mycelialdesigns/Plaice/cad/stubsocketarray.FCStd

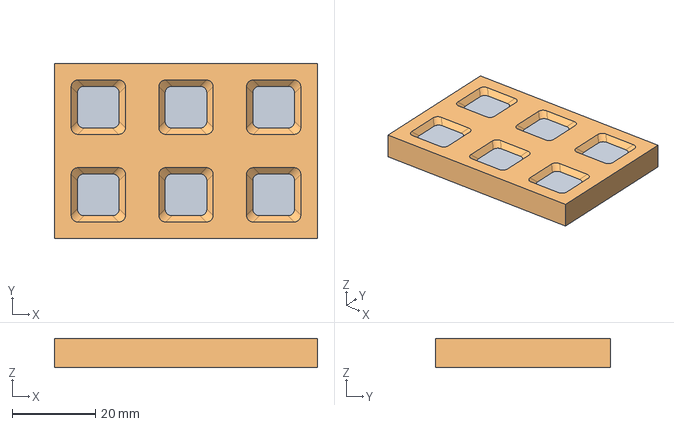
[picture p164: CAD file, 2026-07-09]
cad/stubsocketarray.FCStd
63.0 x 42.0 x 7.00 mm
stubsocketarray
plate_bare001
