mycelialdesigns/Plaice/cad/slide_intruding_xy.FCStd

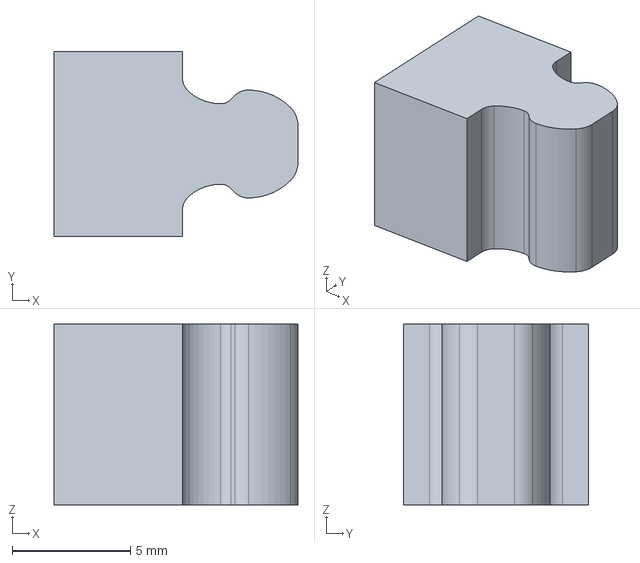
[picture p165: CAD file, 2026-07-09]
cad/slide_intruding_xy.FCStd
10.3 x 7.80 x 7.62 mm
