mycelialdesigns/Plaice/cad/cornerstackingcap.FCStd

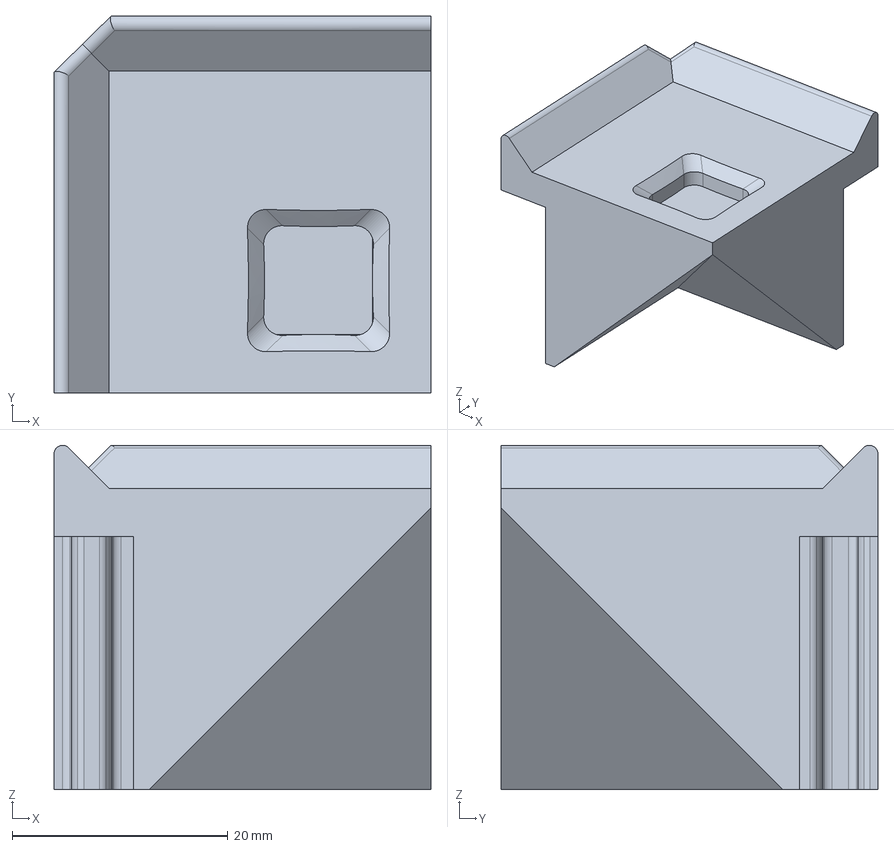
[picture p166: CAD file, 2026-07-09]
cad/cornerstackingcap.FCStd
34.9 x 34.9 x 31.9 mm
