mycelialdesigns/Plaice/cad/slide_protruding_xy.FCStd

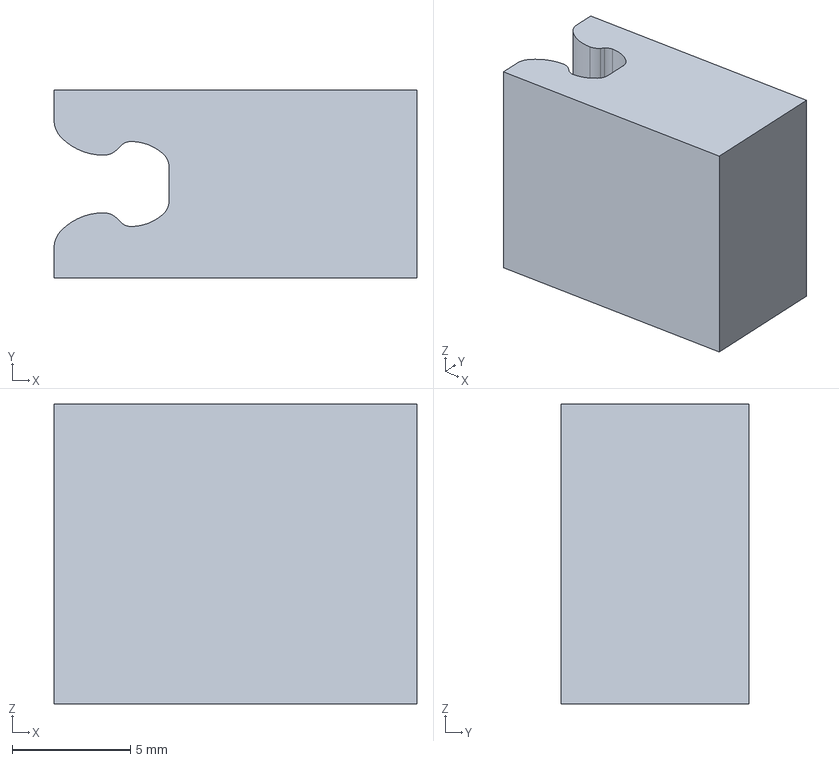
[picture p167: CAD file, 2026-07-09]
cad/slide_protruding_xy.FCStd
15.4 x 7.96 x 12.7 mm
