mycelialdesigns/Plaice/cad/corner.FCStd

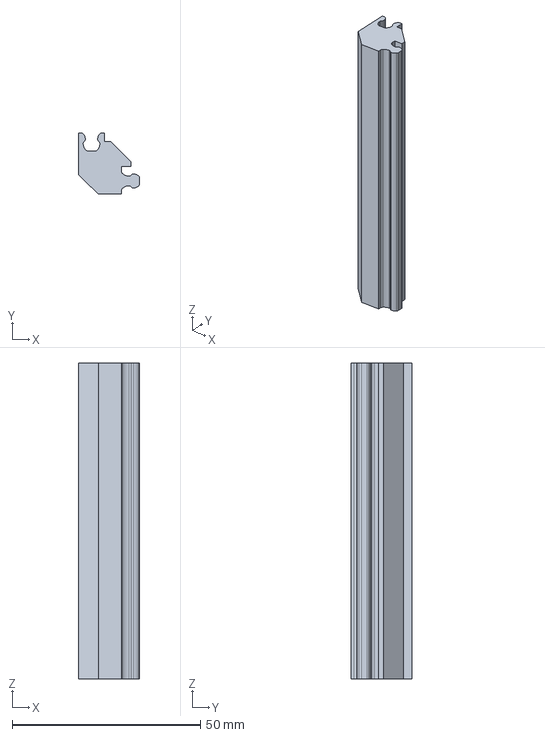
[picture p168: CAD file, 2026-07-09]
cad/corner.FCStd
16.3 x 16.3 x 83.8 mm
