mycelialdesigns/Plaice/cad/plug.FCStd

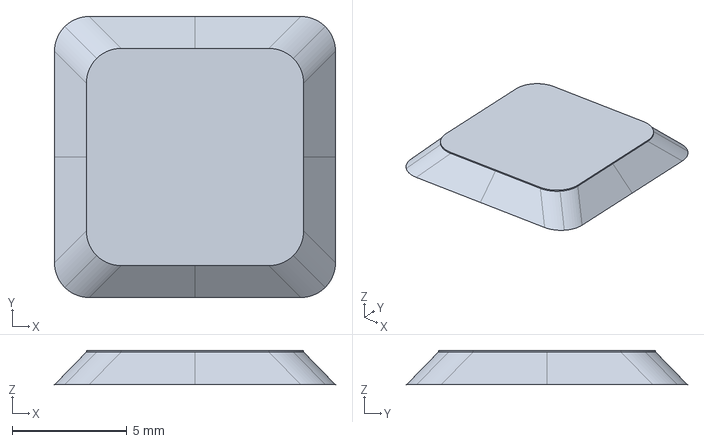
[picture p169: CAD file, 2026-07-09]
cad/plug.FCStd
12.3 x 12.3 x 1.50 mm
