mycelialdesigns/Plaice/cad/plug_nubbed_array.FCStd

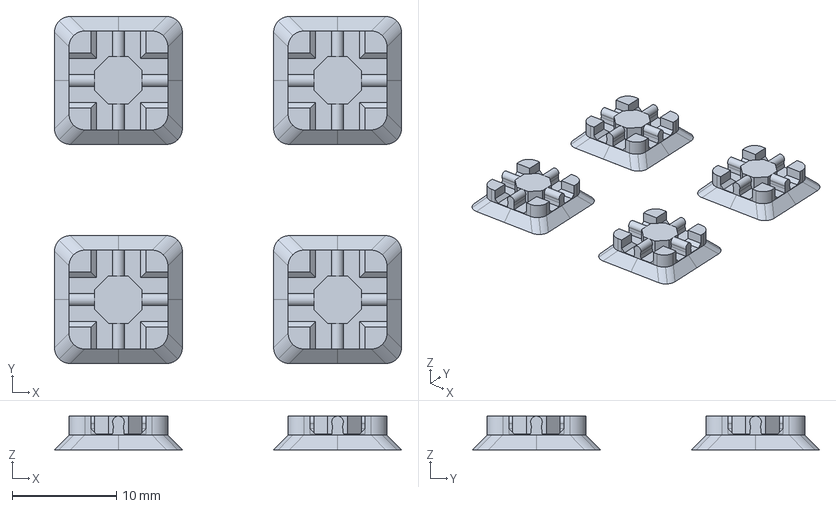
[picture p170: CAD file, 2026-07-09]
cad/plug_nubbed_array.FCStd
33.3 x 33.3 x 3.24 mm
