mycelialdesigns/Plaice/cad/cross_glide.FCStd

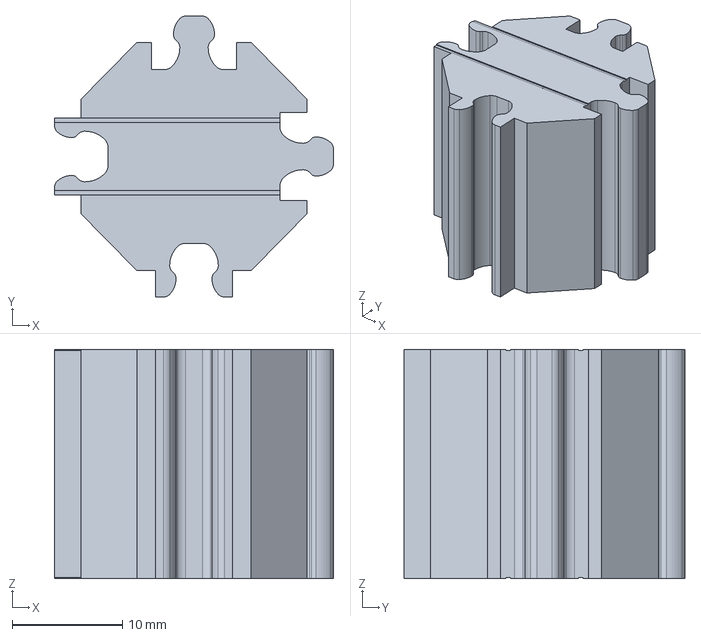
[picture p171: CAD file, 2026-07-09]
cad/cross_glide.FCStd
25.4 x 25.5 x 20.8 mm
