mycelialdesigns/Plaice/cad/tee_slide_intruding.FCStd

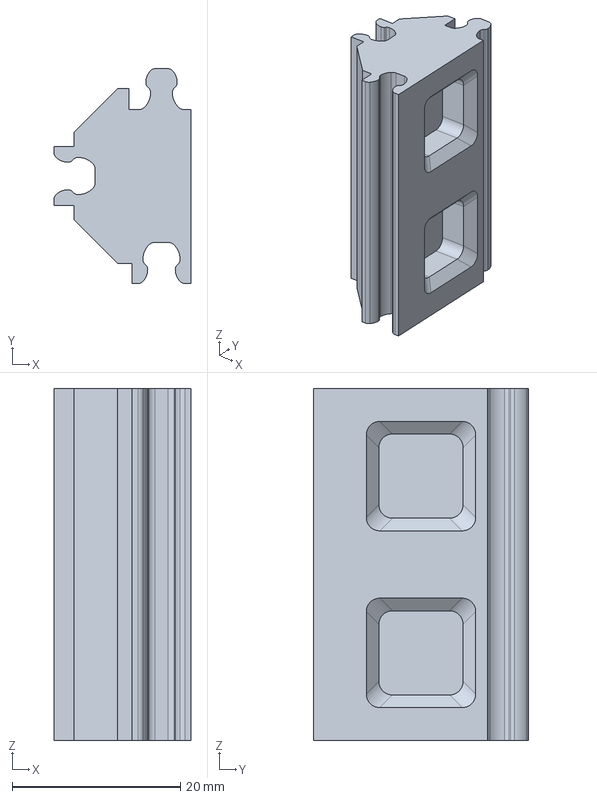
[picture p172: CAD file, 2026-07-09]
cad/tee_slide_intruding.FCStd
16.3 x 25.5 x 41.8 mm
