mycelialdesigns/Plaice/cad/cornerstackingcap_thin.FCStd

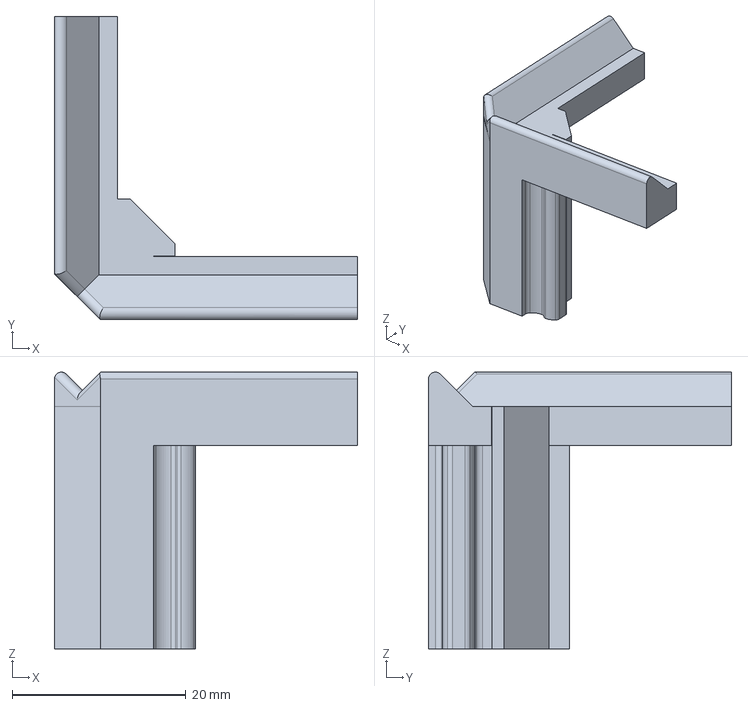
[picture p173: CAD file, 2026-07-09]
cad/cornerstackingcap_thin.FCStd
34.9 x 34.9 x 31.9 mm
