mycelialdesigns/Plaice/cad/plug_nubbed.FCStd

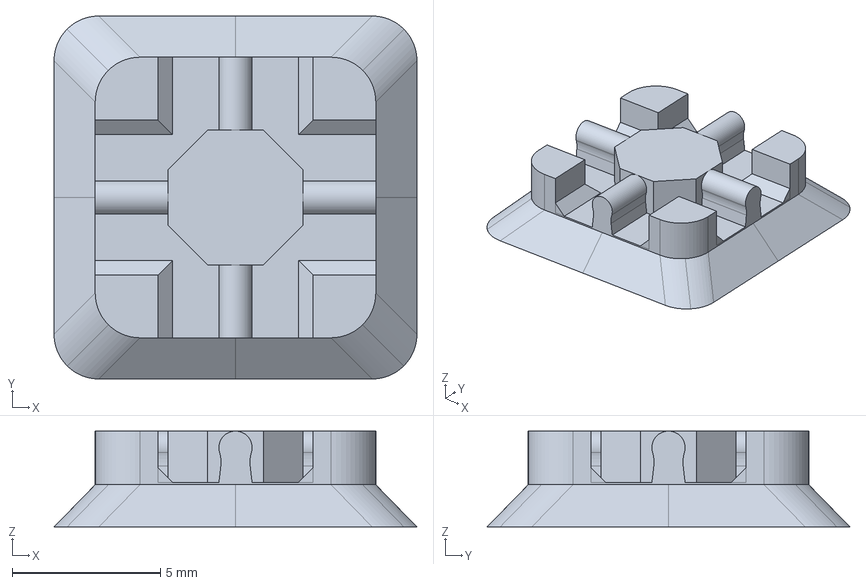
[picture p174: CAD file, 2026-07-09]
cad/plug_nubbed.FCStd
12.3 x 12.3 x 3.24 mm
