mycelialdesigns/Plaice/cad/stackinglip_intruding.FCStd

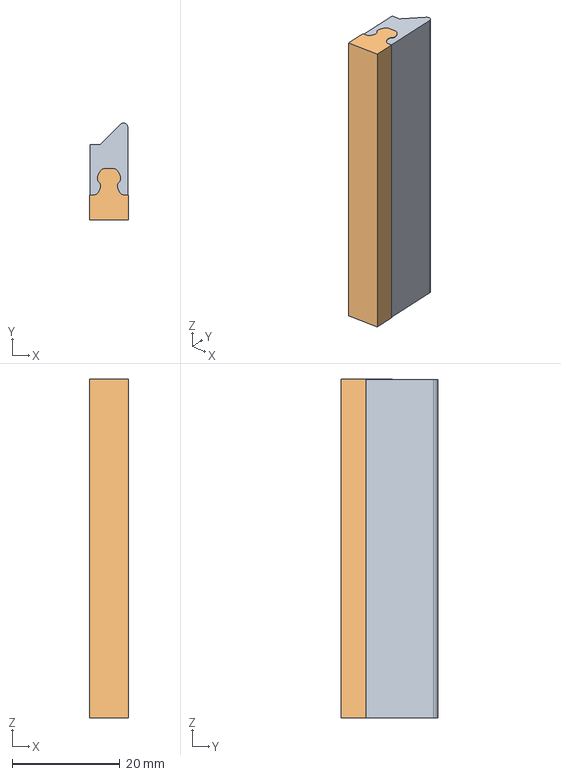
[picture p175: CAD file, 2026-07-06]
cad/stackinglip_intruding.FCStd
7.30 x 18.0 x 63.0 mm
stackinglip_intruding
subtractive
