mycelialdesigns/Plaice/cad/cover_clipped.FCStd

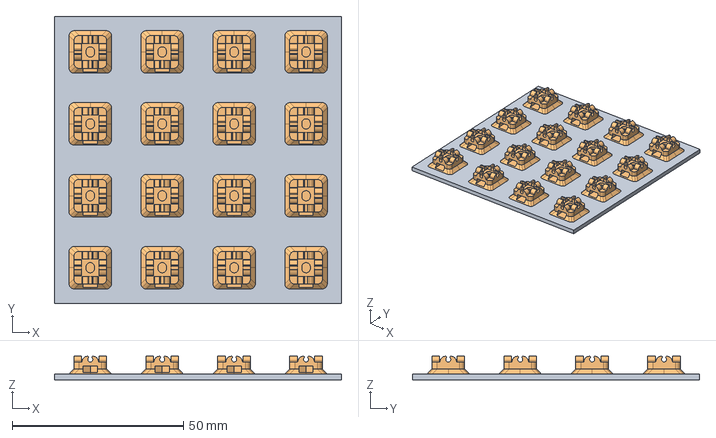
[picture p176: CAD file, 2026-07-06]
cad/cover_clipped.FCStd
83.8 x 83.8 x 6.90 mm
cover_clipped
plug_clipped_array
