mycelialdesigns/Plaice/cad/cornercap_outside.FCStd

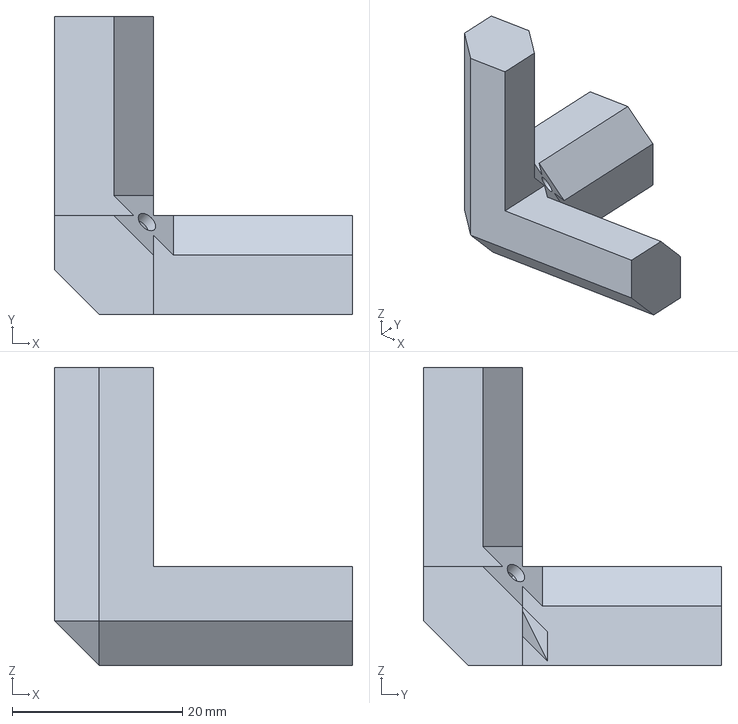
[picture p177: CAD file, 2026-07-06]
cad/cornercap_outside.FCStd
35.0 x 35.0 x 35.0 mm
