mycelialdesigns/Plaice/cad/beam_thru_printable.FCStd

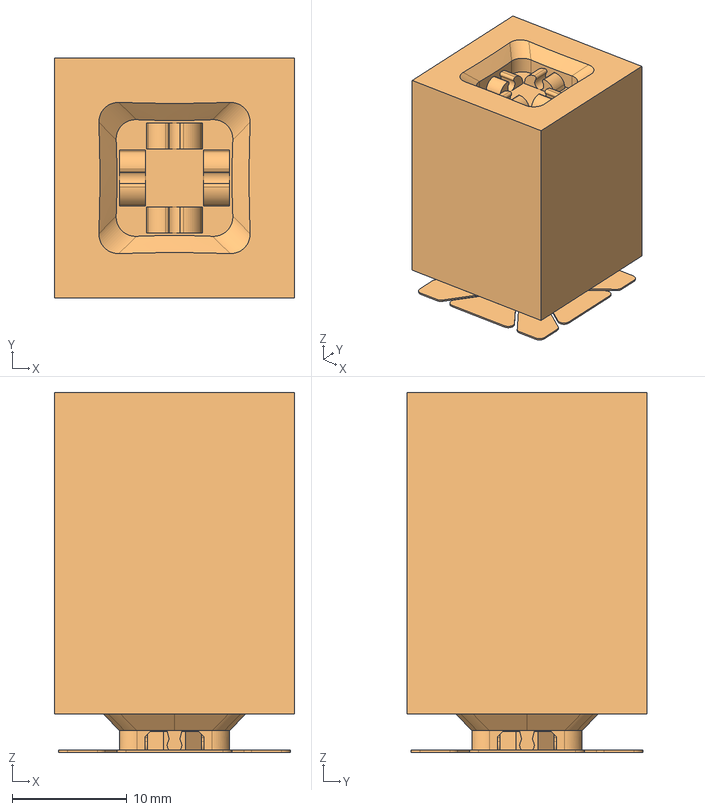
[picture p178: CAD file, 2026-07-06]
cad/beam_thru_printable.FCStd
20.9 x 20.9 x 31.4 mm
beam_thru_printable
beam_printable002
