mycelialdesigns/Plaice/cad/plug_clipped_array.FCStd

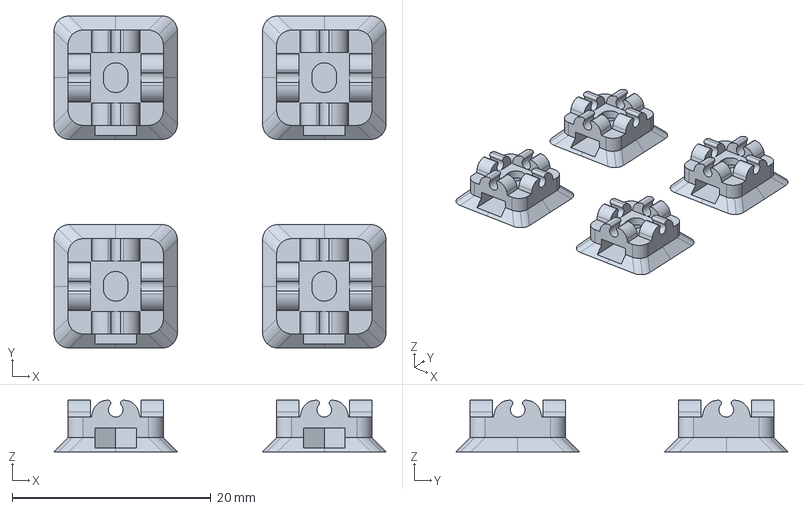
[picture p179: CAD file, 2026-07-06]
cad/plug_clipped_array.FCStd
33.4 x 33.4 x 5.20 mm
