mycelialdesigns/Plaice/cad/nubmouseears_array.FCStd

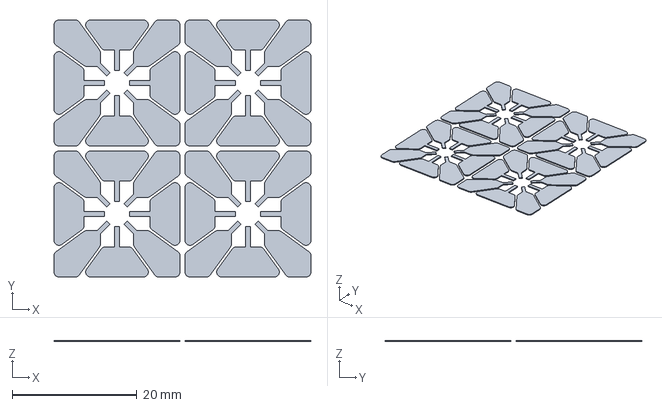
[picture p180: CAD file, 2026-07-06]
cad/nubmouseears_array.FCStd
41.2 x 41.2 x 0.2 mm
