mycelialdesigns/Plaice/cad/tee_glide_protruding_printable.FCStd

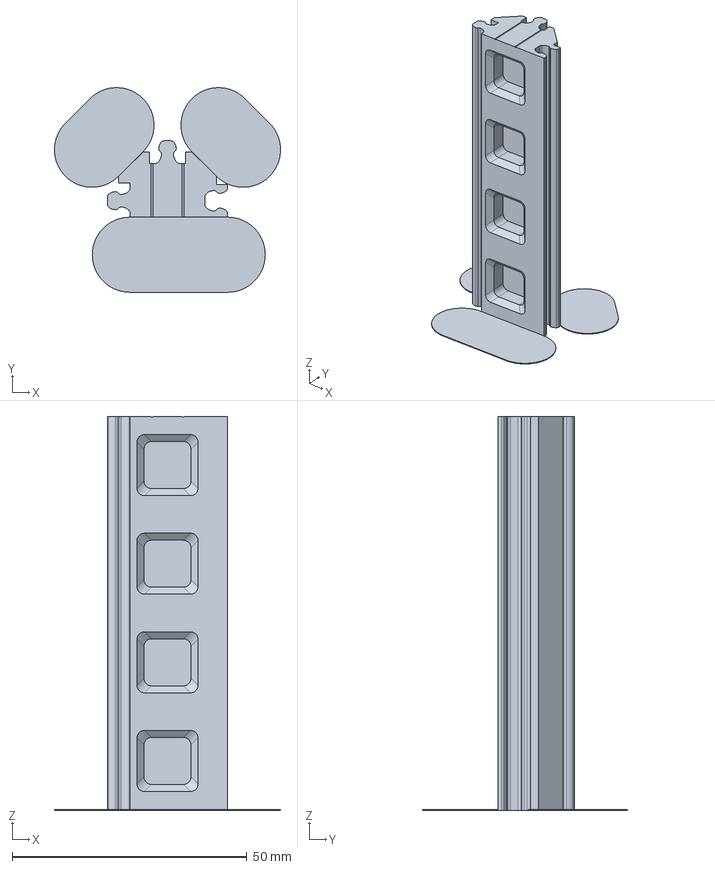
[picture p181: CAD file, 2026-07-06]
cad/tee_glide_protruding_printable.FCStd
48.1 x 43.6 x 83.9 mm
