mycelialdesigns/Plaice/cad/beam.FCStd

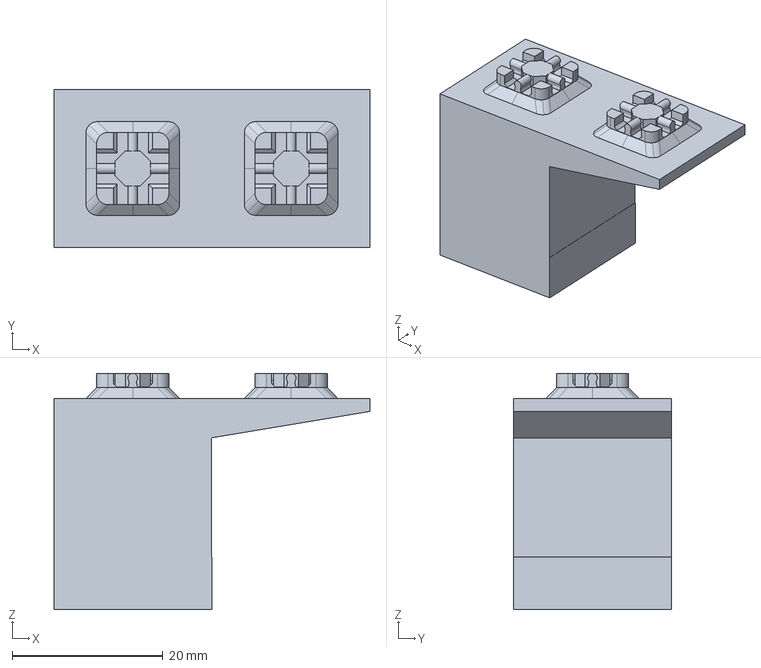
[picture p182: CAD file, 2026-07-06]
cad/beam.FCStd
41.9 x 20.9 x 31.4 mm
