mycelialdesigns/Plaice/cad/slide_intruding.FCStd

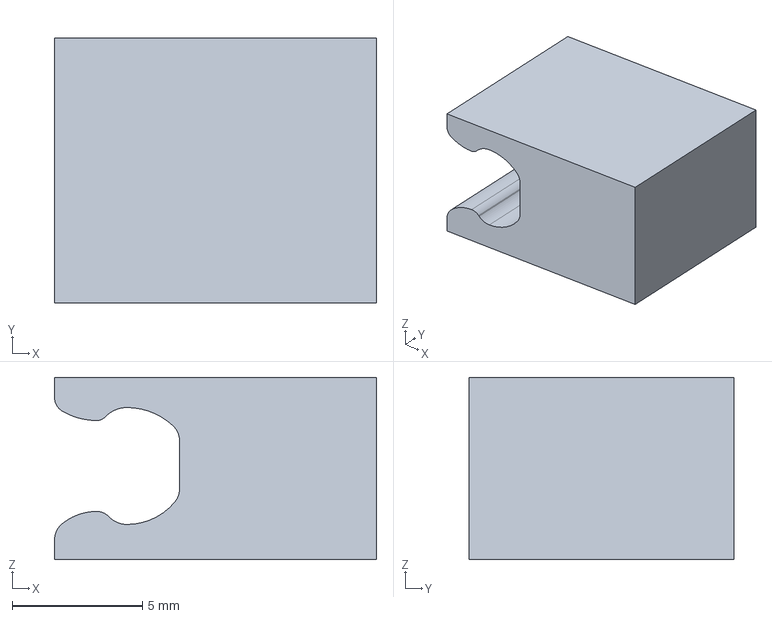
[picture p183: CAD file, 2026-07-06]
cad/slide_intruding.FCStd
12.4 x 10.2 x 7.00 mm
