mycelialdesigns/Plaice/cad/hinge.FCStd

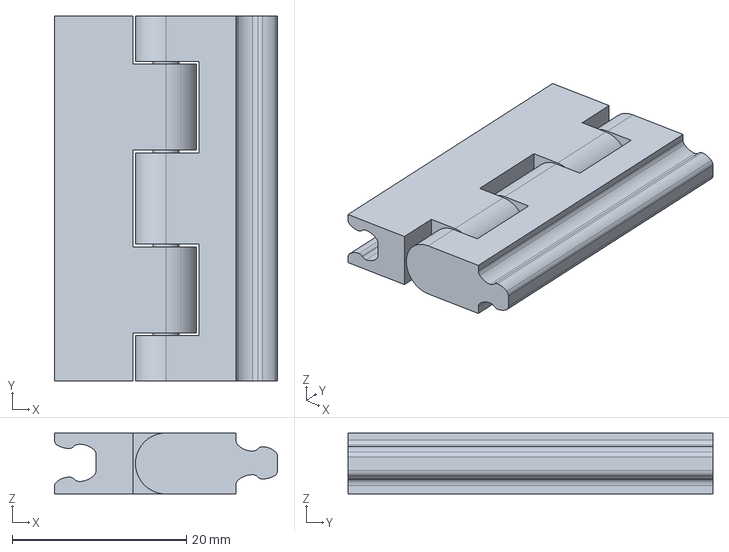
[picture p184: CAD file, 2026-07-06]
cad/hinge.FCStd
25.7 x 41.9 x 7.00 mm
