mycelialdesigns/Plaice/cad/tee_mouseears.FCStd

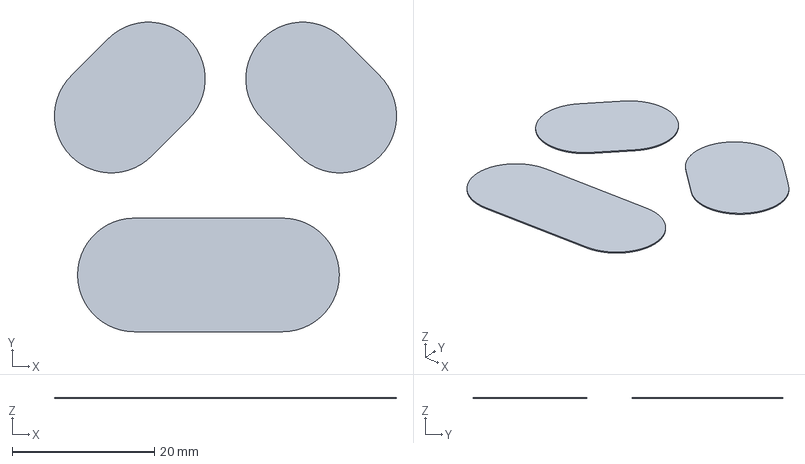
[picture p185: CAD file, 2026-07-06]
cad/tee_mouseears.FCStd
48.1 x 43.6 x 0.2 mm
