mycelialdesigns/Plaice/cad/corner_printable.FCStd

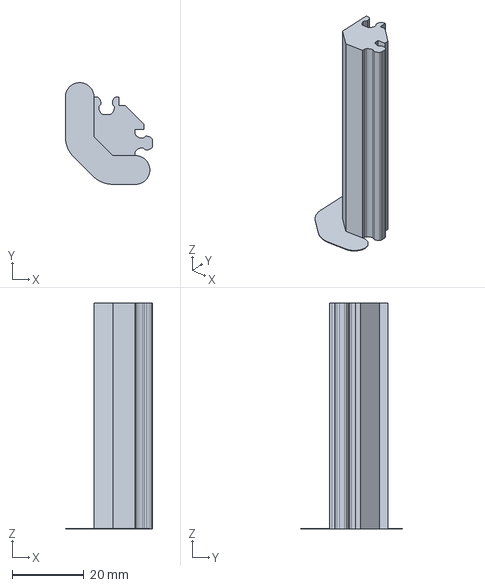
[picture p186: CAD file, 2026-07-06]
cad/corner_printable.FCStd
24.3 x 28.3 x 62.9 mm
