mycelialdesigns/Plaice/cad/plate_overmold_side.FCStd

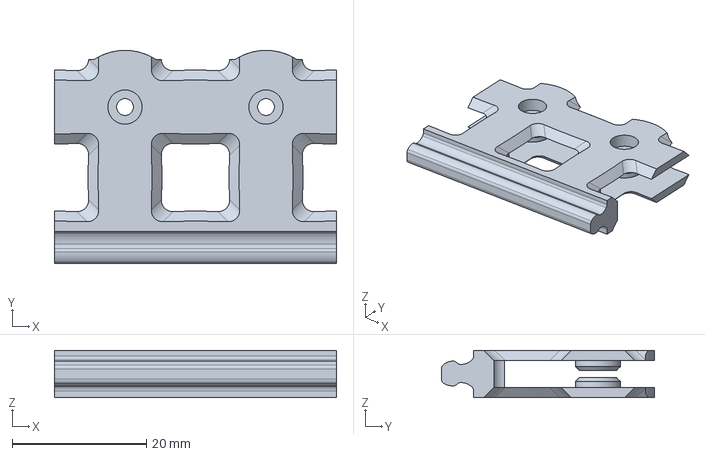
[picture p187: CAD file, 2026-07-06]
cad/plate_overmold_side.FCStd
42.0 x 31.8 x 7.00 mm
