mycelialdesigns/Plaice/cad/tee_glide_intruding_printable.FCStd

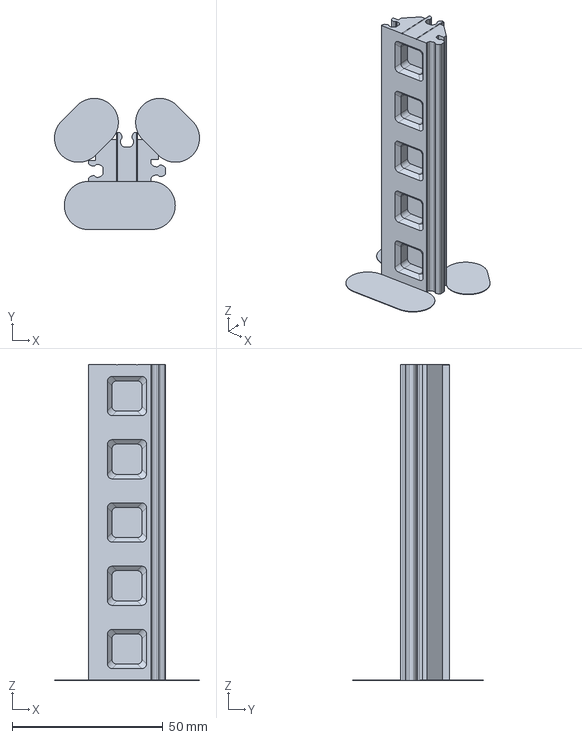
[picture p188: CAD file, 2026-07-06]
cad/tee_glide_intruding_printable.FCStd
48.1 x 43.6 x 104.9 mm
