mycelialdesigns/Plaice/cad/lasercut.FCStd

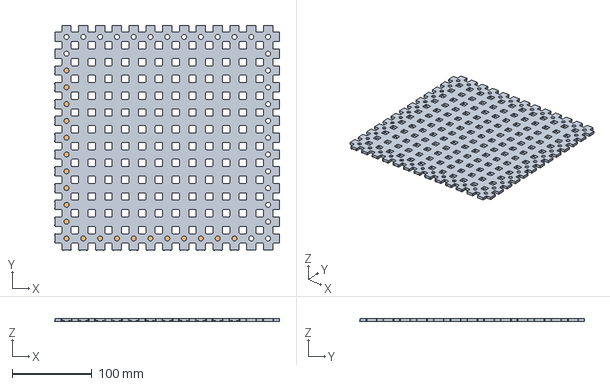
[picture p189: CAD file, 2026-07-06]
cad/lasercut.FCStd
281.3 x 281.3 x 4.00 mm
middle
top
