mycelialdesigns/Plaice/cad/tee_slide_intruding_printable.FCStd

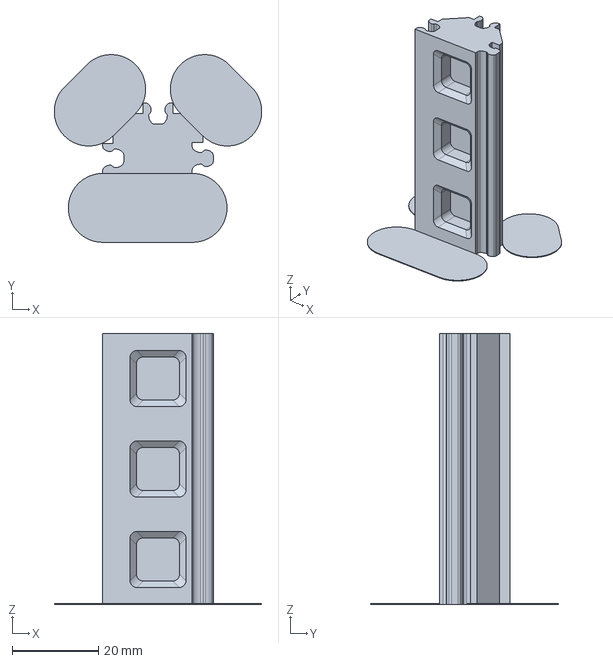
[picture p190: CAD file, 2026-07-06]
cad/tee_slide_intruding_printable.FCStd
48.1 x 43.6 x 62.9 mm
