mycelialdesigns/Plaice/cad/stackingpeg.FCStd

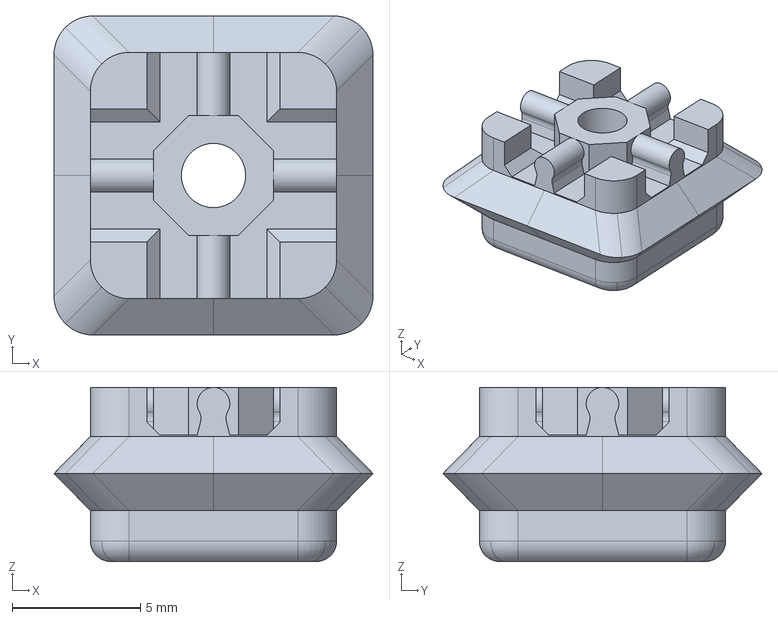
[picture p191: CAD file, 2026-07-06]
cad/stackingpeg.FCStd
12.4 x 12.4 x 6.78 mm
