mycelialdesigns/Plaice/cad/plate_routed.FCStd

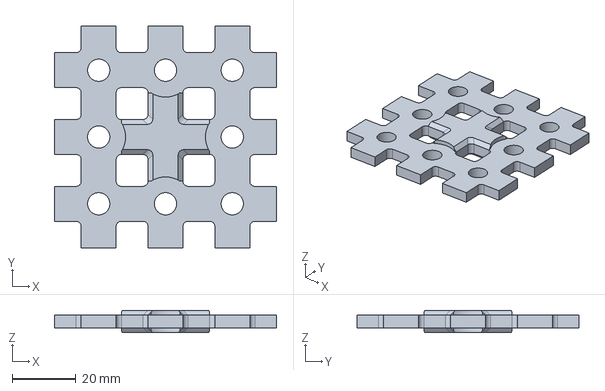
[picture p192: CAD file, 2026-07-06]
cad/plate_routed.FCStd
69.8 x 69.8 x 7.00 mm
