mycelialdesigns/Plaice/cad/manualrouterjigs.FCStd

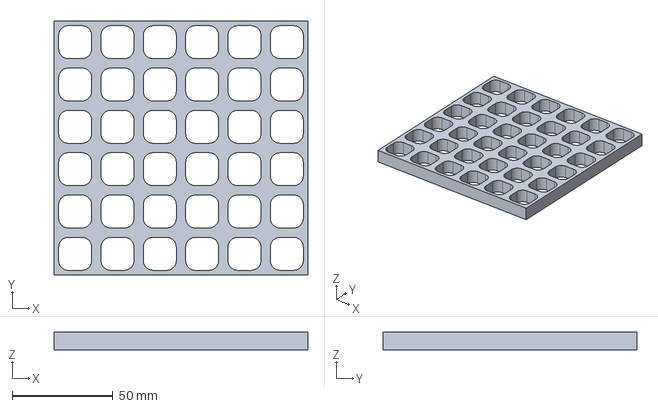
[picture p193: CAD file, 2026-07-06]
cad/manualrouterjigs.FCStd
126.0 x 126.0 x 8.89 mm
