mycelialdesigns/Plaice/cad/plate_overmold_corner.FCStd

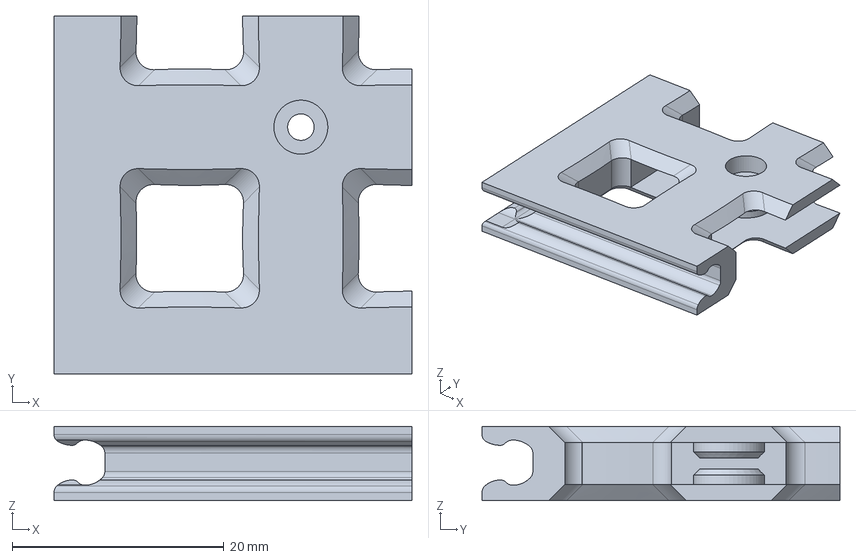
[picture p194: CAD file, 2026-07-06]
cad/plate_overmold_corner.FCStd
33.8 x 33.8 x 7.00 mm
