mycelialdesigns/Plaice/cad/beam_printable.FCStd

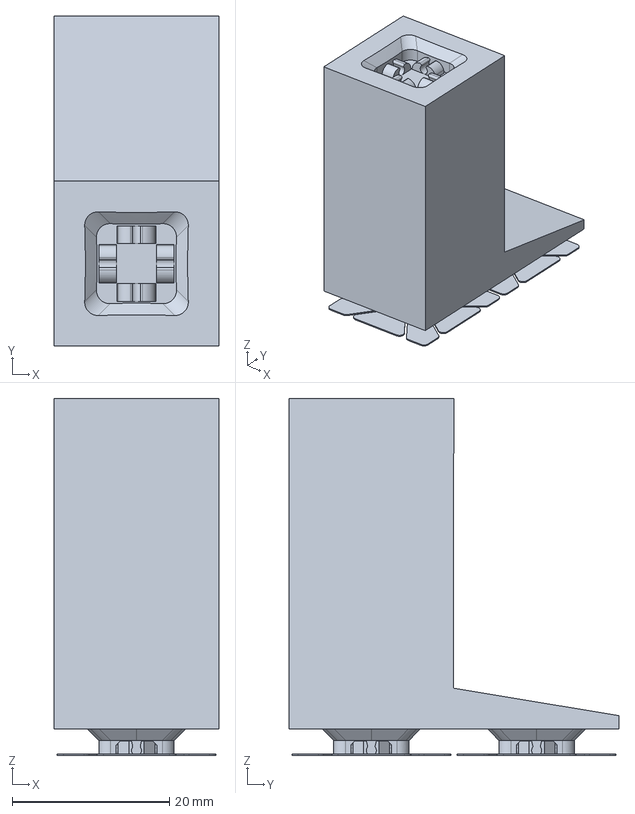
[picture p195: CAD file, 2026-07-06]
cad/beam_printable.FCStd
20.9 x 41.9 x 45.4 mm
