mycelialdesigns/Plaice/cad/backing_nubbed.FCStd

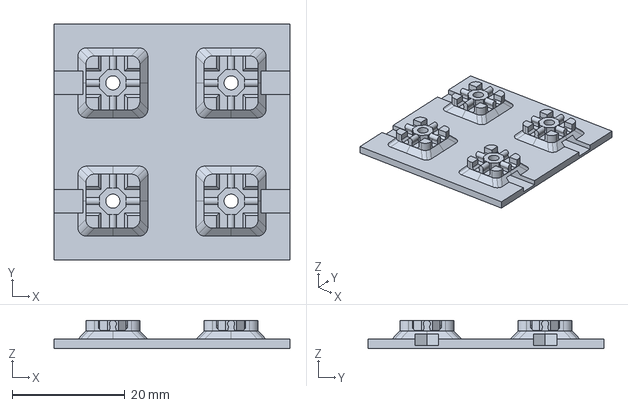
[picture p196: CAD file, 2026-07-06]
cad/backing_nubbed.FCStd
41.9 x 41.9 x 5.05 mm
