mycelialdesigns/Plaice/cad/backing_clipped.FCStd

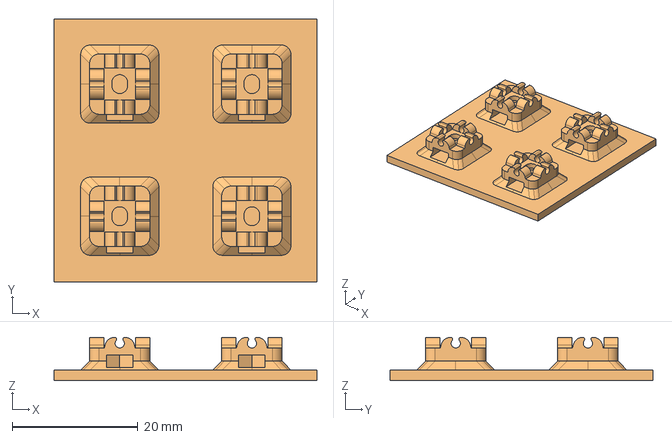
[picture p197: CAD file, 2026-07-06]
cad/backing_clipped.FCStd
41.8 x 41.8 x 6.90 mm
backing_clipped
cover_clipped001
