mycelialdesigns/Plaice/cad/cover_nubbed.FCStd

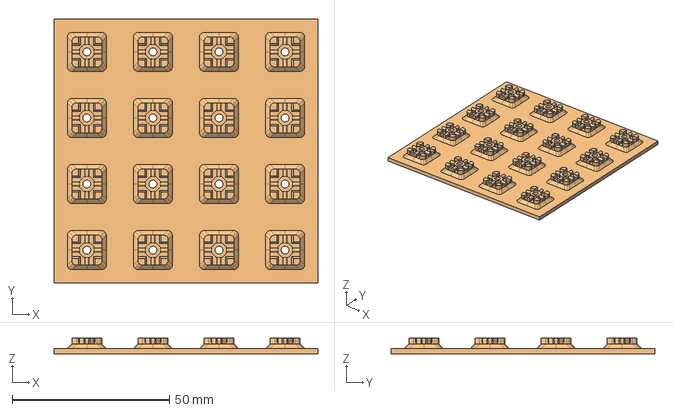
[picture p198: CAD file, 2026-07-06]
cad/cover_nubbed.FCStd
83.9 x 83.9 x 5.05 mm
cover_nubbed
cover_nubbed_base001
