mycelialdesigns/Plaice/cad/cornercap_inside.FCStd

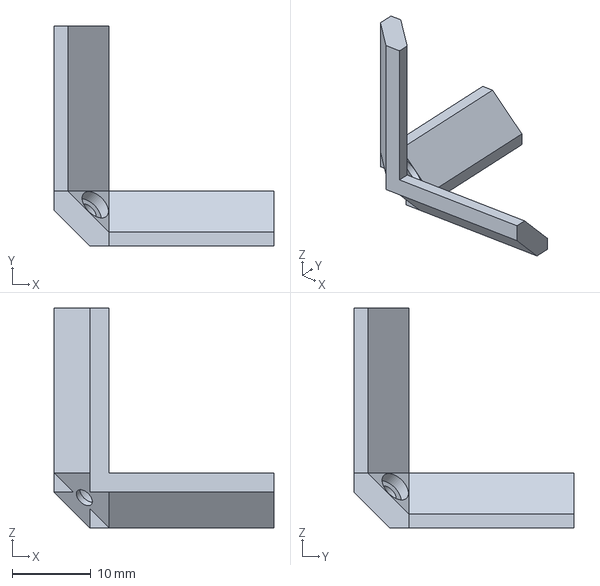
[picture p199: CAD file, 2026-07-06]
cad/cornercap_inside.FCStd
28.0 x 28.0 x 28.0 mm
