mycelialdesigns/Plaice/cad/tee_slide_protruding_printable.FCStd

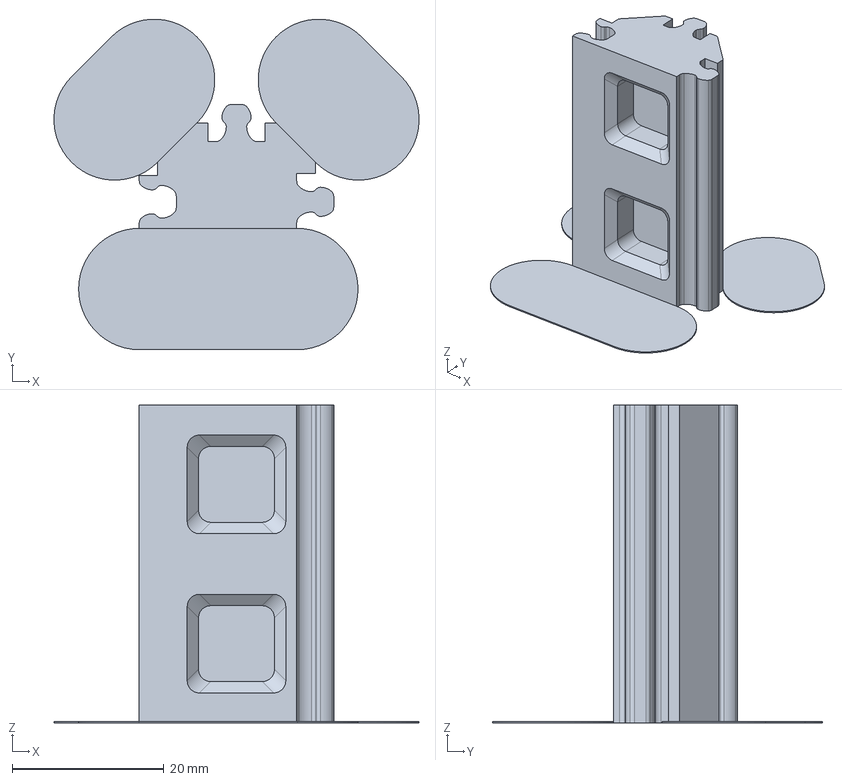
[picture p200: CAD file, 2026-07-06]
cad/tee_slide_protruding_printable.FCStd
48.1 x 43.6 x 41.9 mm
