mycelialdesigns/Plaice/cad/plug_clipped.FCStd

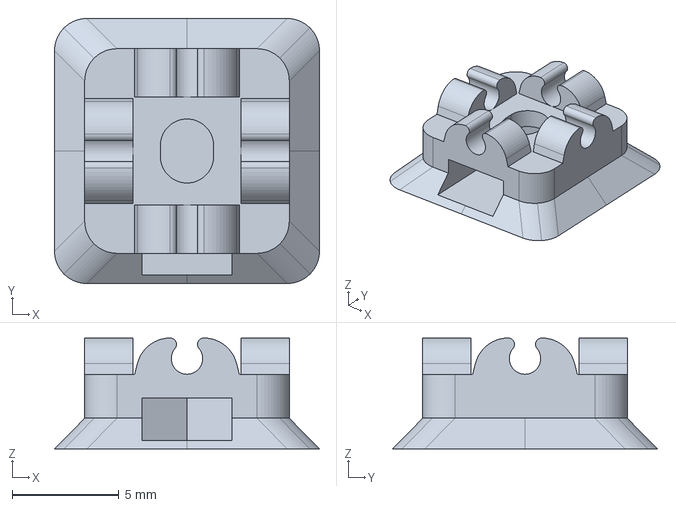
[picture p201: CAD file, 2026-07-06]
cad/plug_clipped.FCStd
12.4 x 12.4 x 5.20 mm
