mycelialdesigns/Plaice/cad/stackinglip_base.FCStd

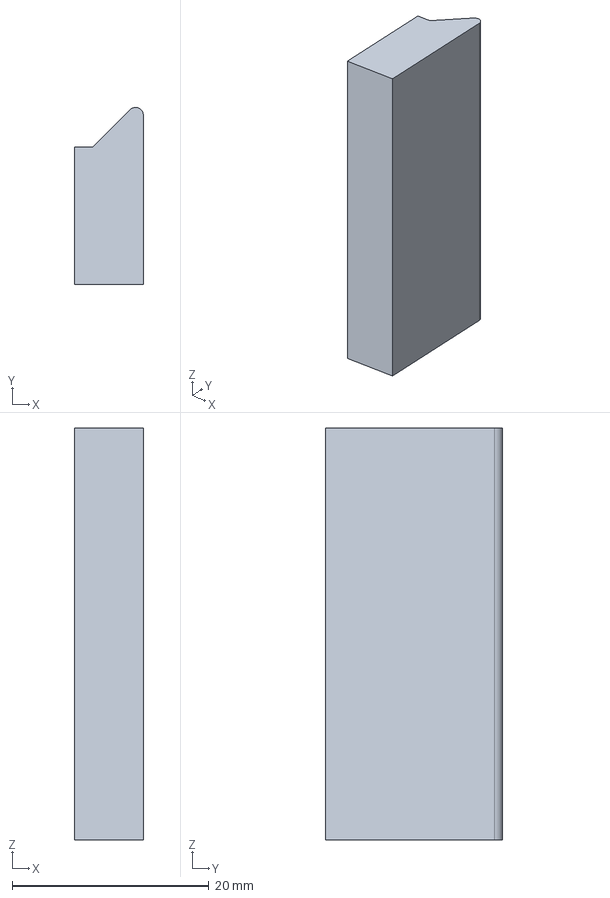
[picture p202: CAD file, 2026-07-06]
cad/stackinglip_base.FCStd
7.00 x 18.0 x 41.9 mm
