mycelialdesigns/Plaice/cad/nubmouseears.FCStd

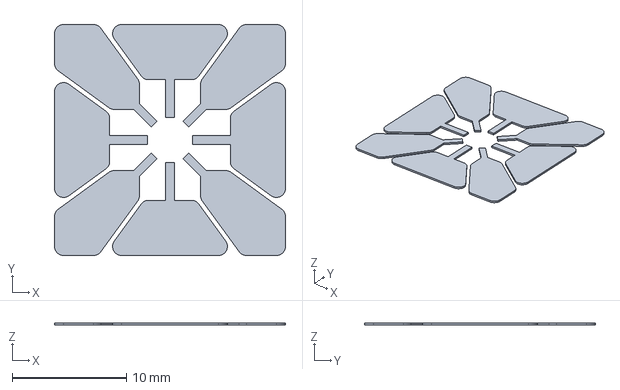
[picture p203: CAD file, 2026-07-06]
cad/nubmouseears.FCStd
20.2 x 20.2 x 0.2 mm
