mycelialdesigns/Plaice/cad/stackinglip_protruding.FCStd

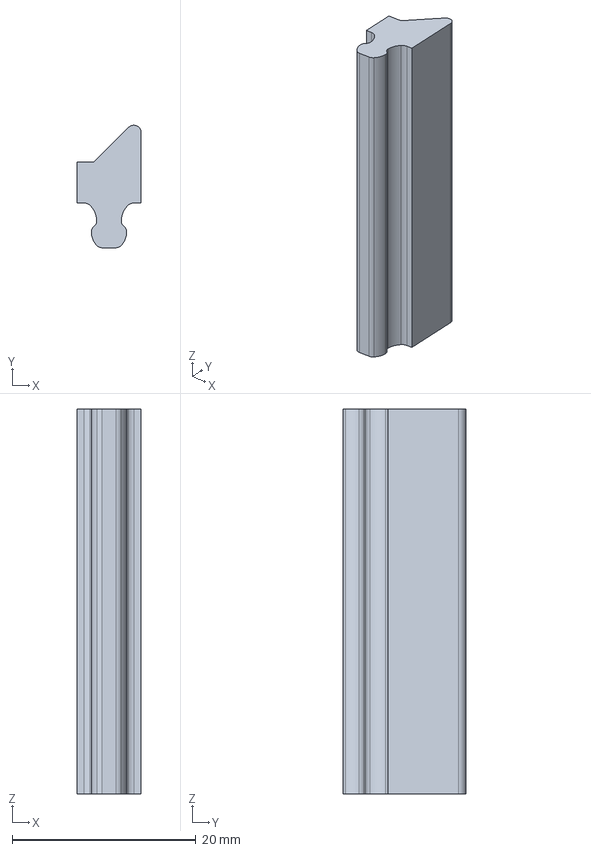
[picture p204: CAD file, 2026-07-06]
cad/stackinglip_protruding.FCStd
7.00 x 13.3 x 41.9 mm
