mycelialdesigns/Plaice/cad/thrunub_printable.FCStd

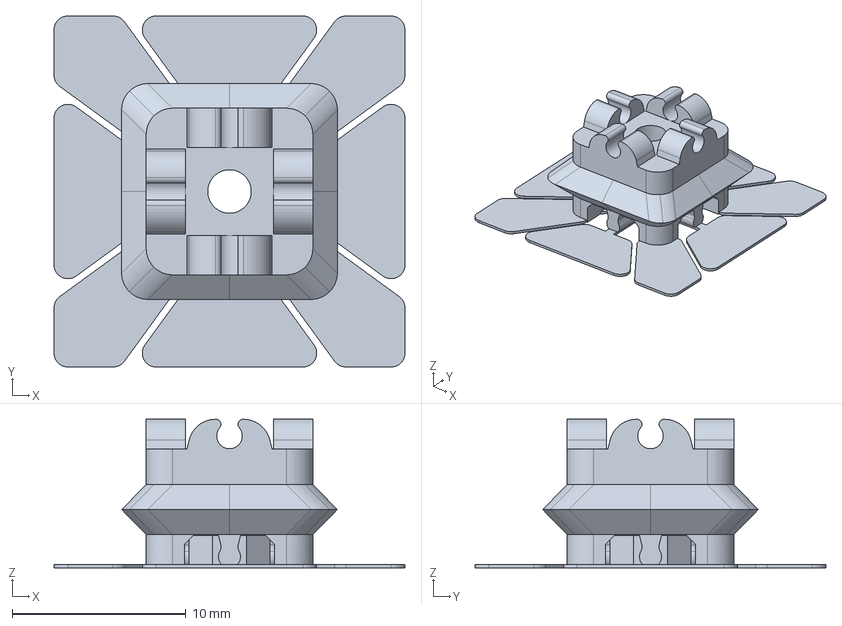
[picture p205: CAD file, 2026-07-06]
cad/thrunub_printable.FCStd
20.2 x 20.2 x 8.55 mm
