mycelialdesigns/Plaice/cad/opengridfundamentalunit.FCStd

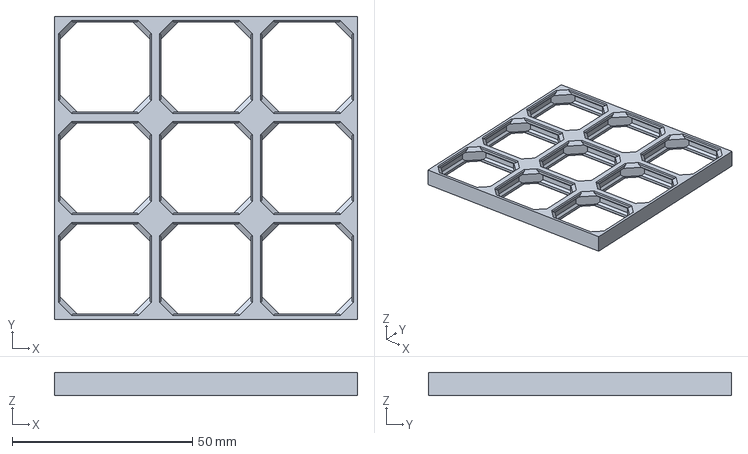
[picture p206: CAD file, 2026-07-01]
cad/opengridfundamentalunit.FCStd
84.0 x 84.0 x 6.51 mm
