mycelialdesigns/Plaice/cad/opengridlitesnapfromstep.FCStd

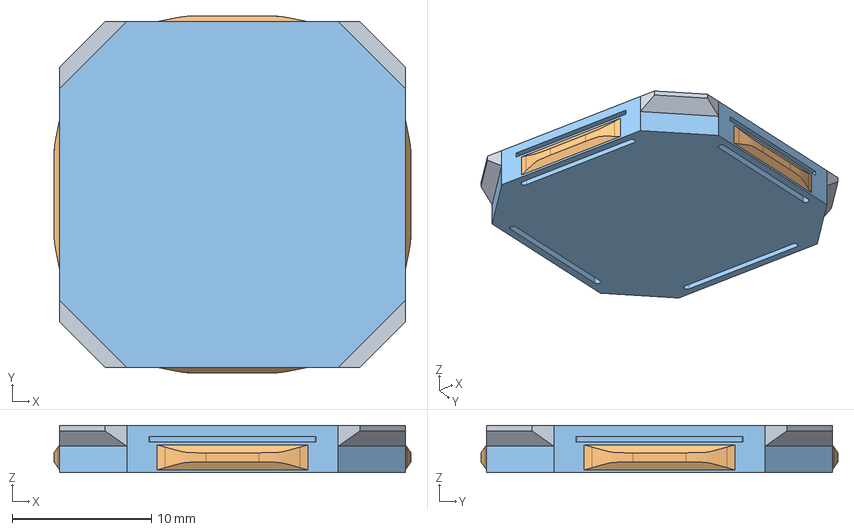
[picture p207: CAD file, 2026-07-01]
cad/opengridlitesnapfromstep.FCStd
25.6 x 25.6 x 3.40 mm
Side Holders
Snap
