mycelialdesigns/Plaice/cad/opengridborder.FCStd

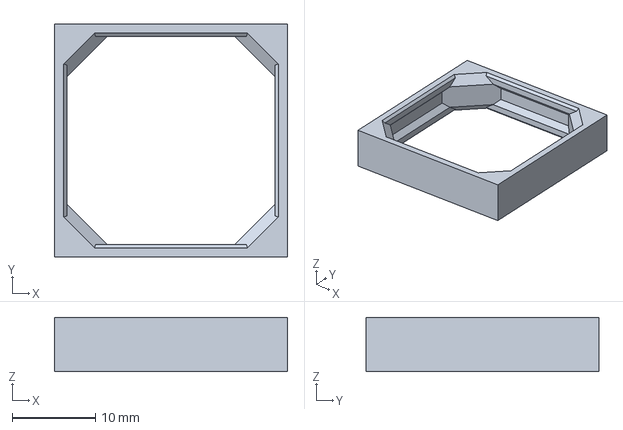
[picture p208: CAD file, 2026-07-01]
cad/opengridborder.FCStd
28.0 x 28.0 x 6.51 mm
